CruvixDev/weather-station-poc/3d_models/S2-LPQTR.stp

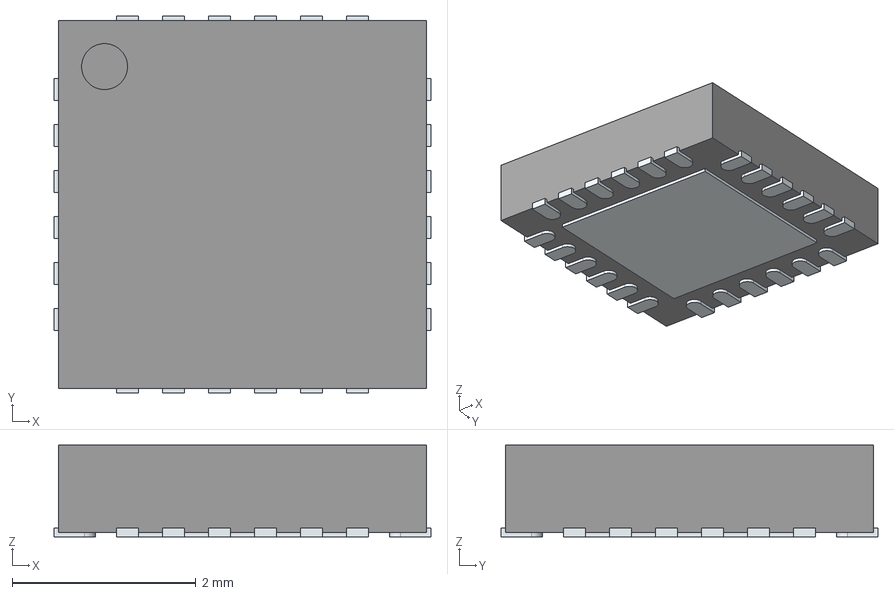
[picture p19: CAD file, 2025-10-29]
3d_models/S2-LPQTR.stp
4.10 x 4.10 x 1.00 mm
ThermalPin
PinsArrayLR
PinsArrayTB
