CruvixDev/weather-station-poc/3d_models/STL11N3LLH6.stp

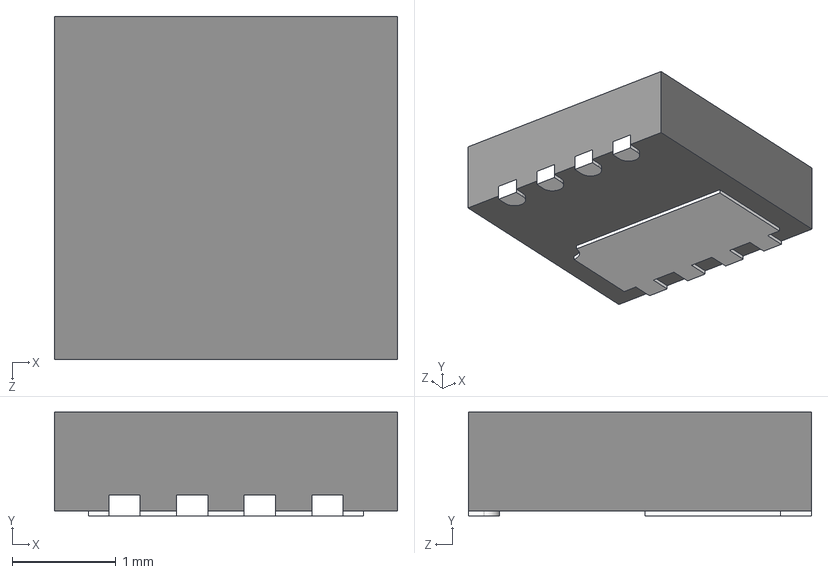
[picture p20: CAD file, 2025-10-29]
3d_models/STL11N3LLH6.stp
3.30 x 1 x 3.30 mm
