CruvixDev/weather-station-poc/3d_models/USBLC6-2SC6.stp

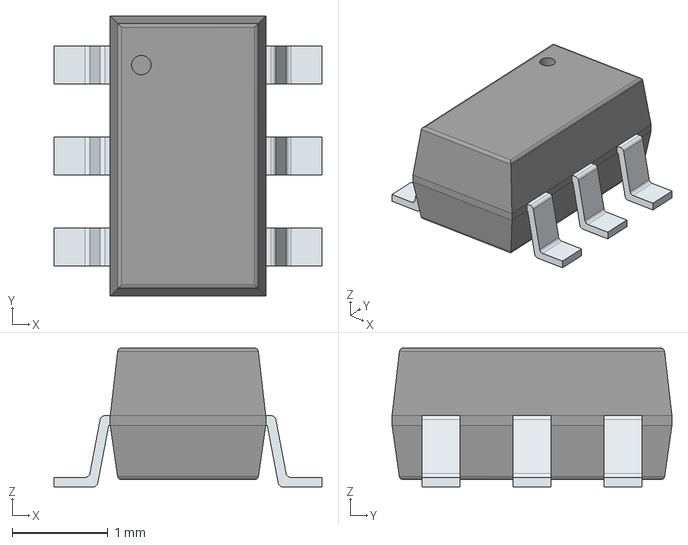
[picture p21: CAD file, 2025-10-29]
3d_models/USBLC6-2SC6.stp
2.80 x 2.92 x 1.45 mm
PinsArrayLR
