CruvixDev/weather-station-poc/3d_models/TCPP01-M12.stp

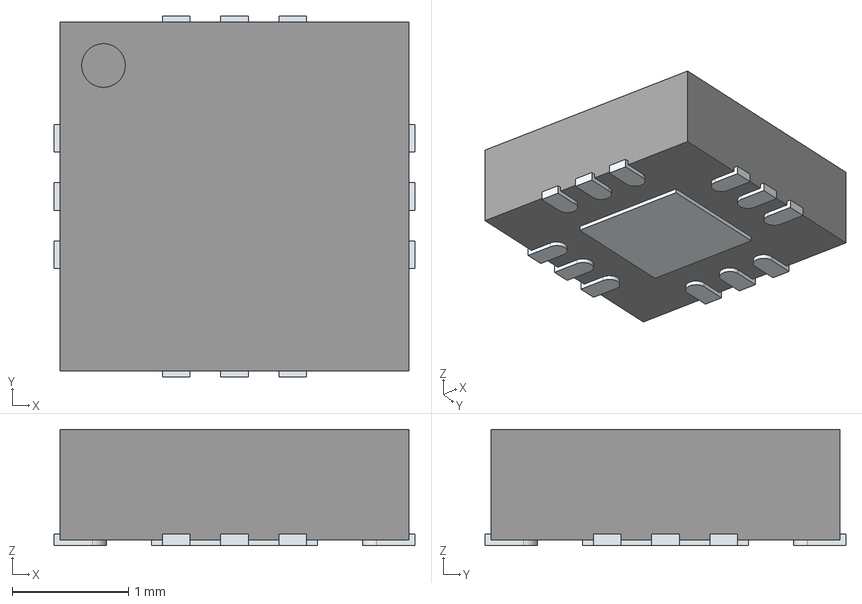
[picture p22: CAD file, 2025-10-29]
3d_models/TCPP01-M12.stp
3.10 x 3.10 x 1.00 mm
ThermalPin
PinsArrayLR
PinsArrayTB
