CruvixDev/weather-station-poc/3d_models/BMP581.stp

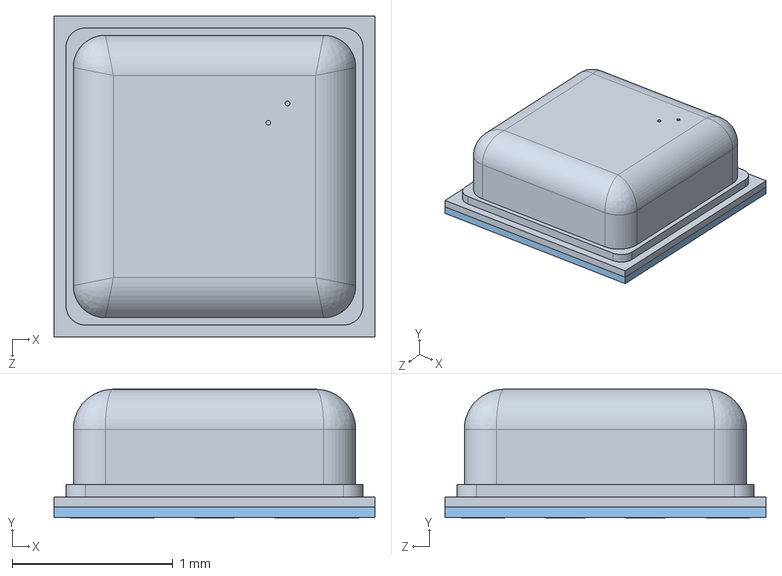
[picture p23: CAD file, 2025-10-29]
3d_models/BMP581.stp
2.00 x 0.801 x 2.00 mm
